tekdemo/PCB-Crown/gerber-previews/crown-B.board-bottom.diff.png

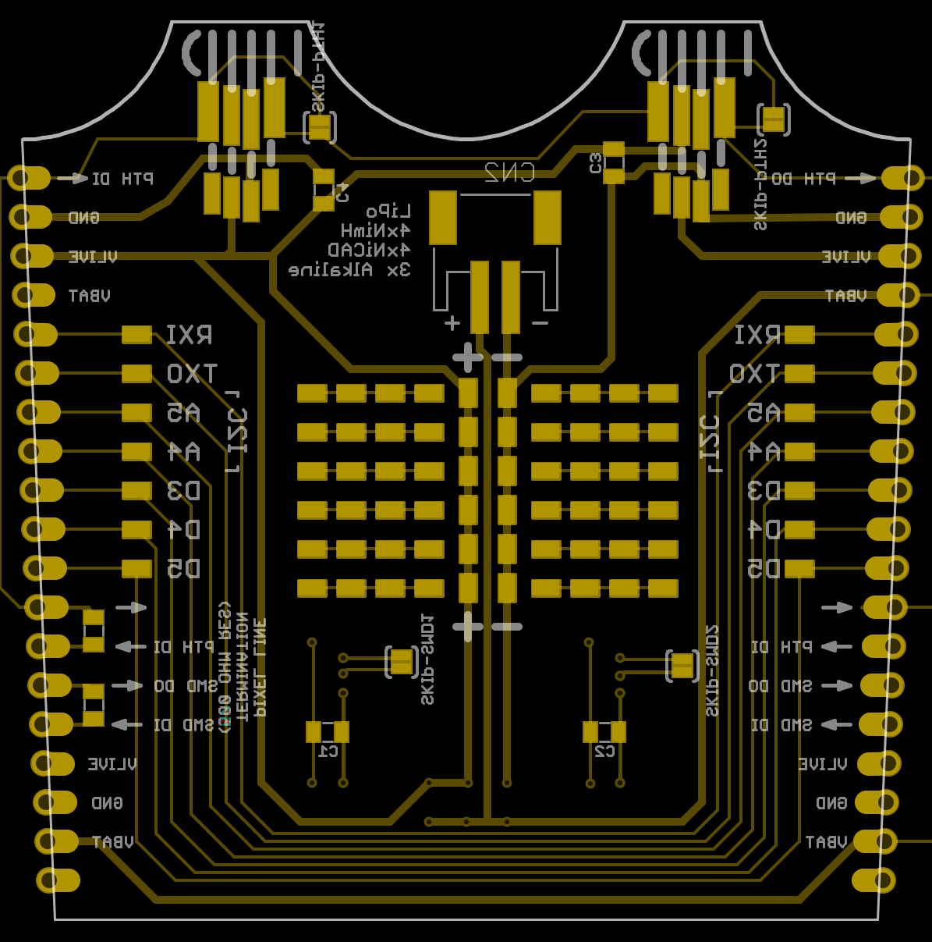
gerber-previews/crown-B.board-bottom.diff.png
