tekdemo/PCB-Crown/gerber-previews/crown-B.board-top.diff.png

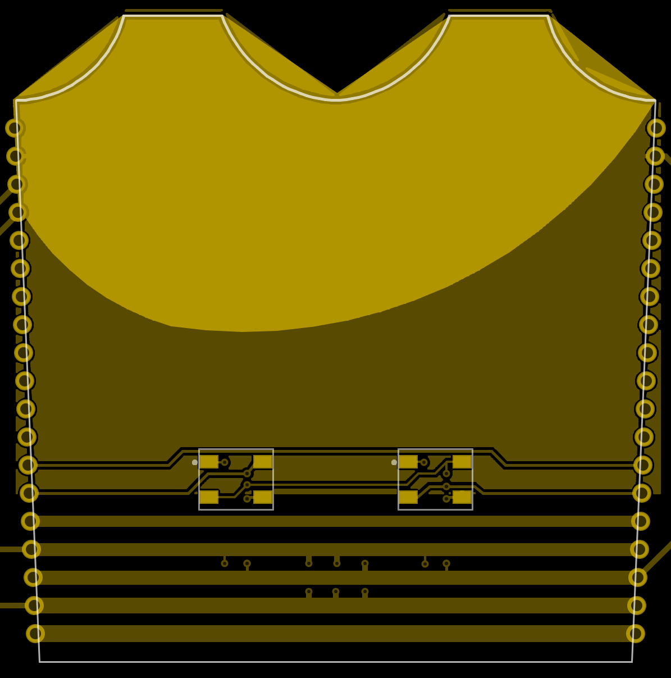
gerber-previews/crown-B.board-top.diff.png
