tekdemo/PCB-Crown/gerber-previews/crown-B.boardoutline.diff.png

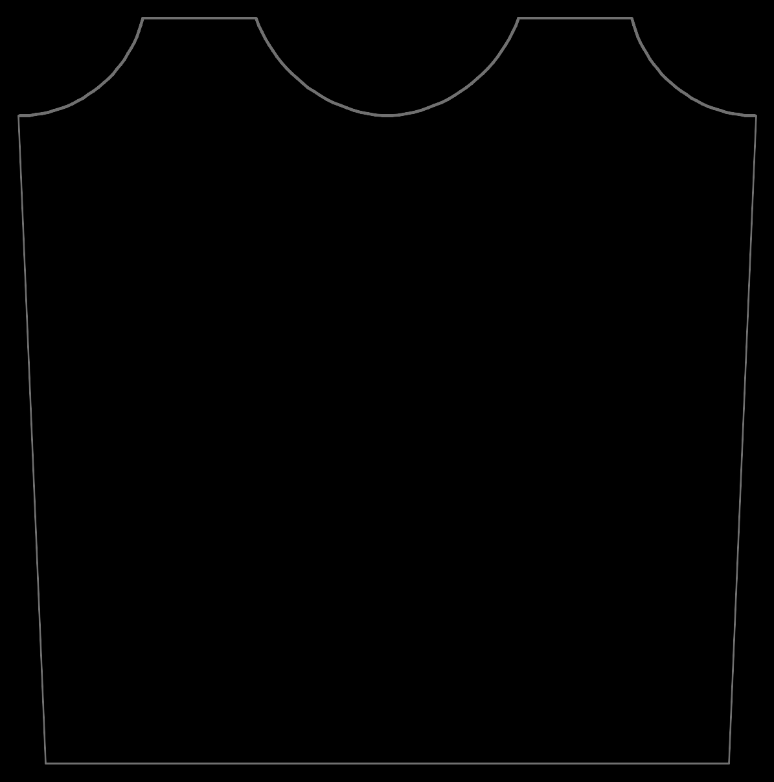
gerber-previews/crown-B.boardoutline.diff.png
