tekdemo/PCB-Crown/gerber-previews/crown-B.bottomlayer.diff.png

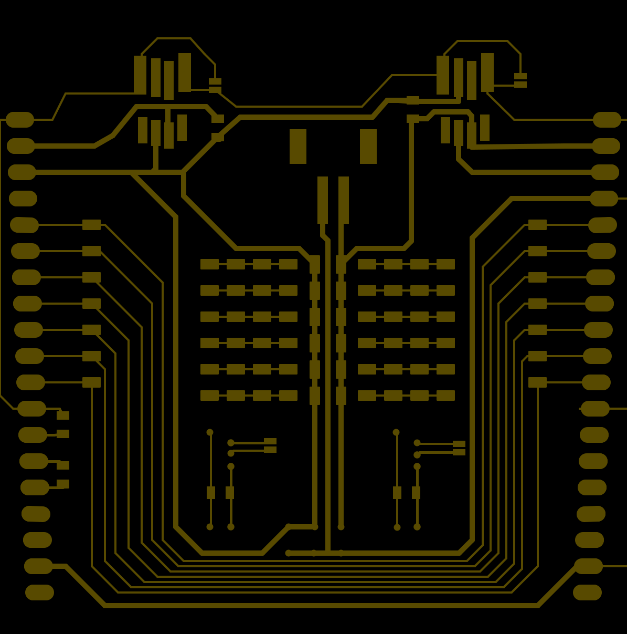
gerber-previews/crown-B.bottomlayer.diff.png
