tekdemo/PCB-Crown/gerber-previews/crown-B.bottomsilkscreen.diff.png

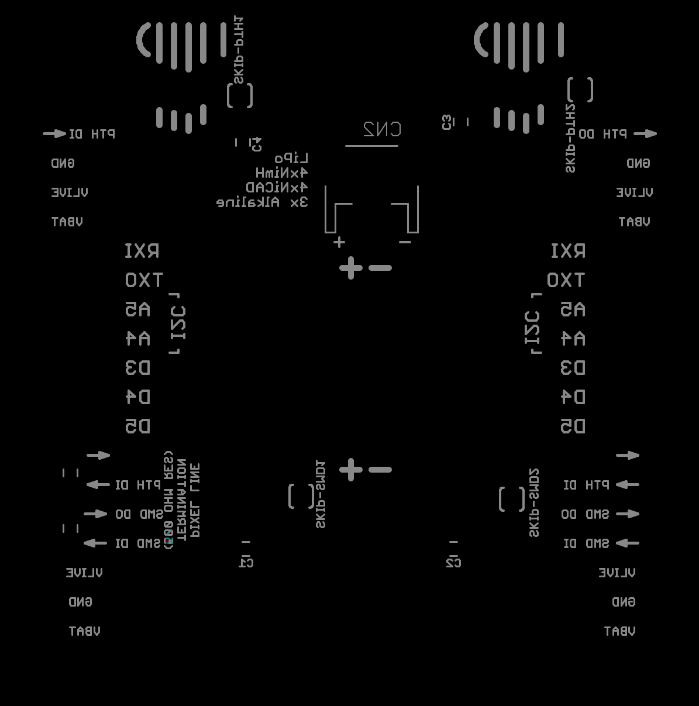
gerber-previews/crown-B.bottomsilkscreen.diff.png
