tekdemo/PCB-Crown/gerber-previews/crown-B.bottomstopmask.diff.png

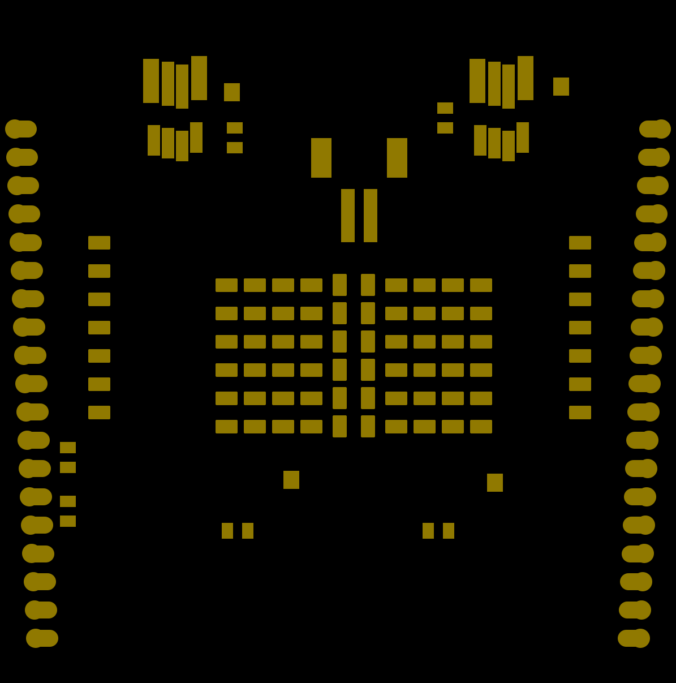
gerber-previews/crown-B.bottomstopmask.diff.png
