tekdemo/PCB-Crown/gerber-previews/crown-B.drills.diff.png

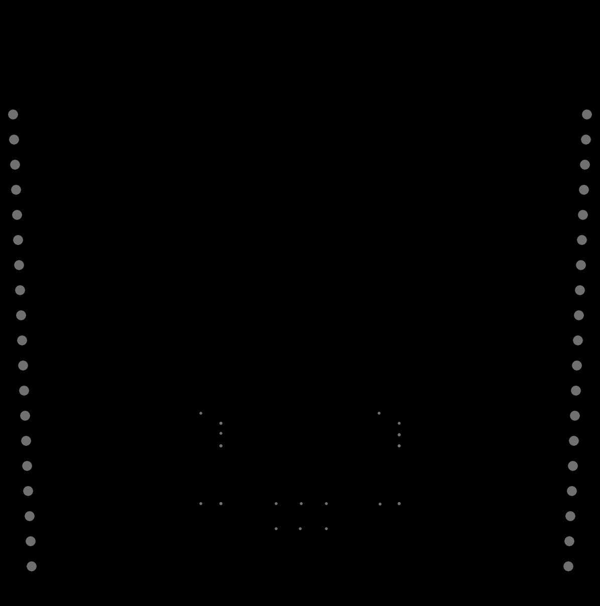
gerber-previews/crown-B.drills.diff.png
