tekdemo/PCB-Crown/gerber-previews/crown-B.toplayer.diff.png

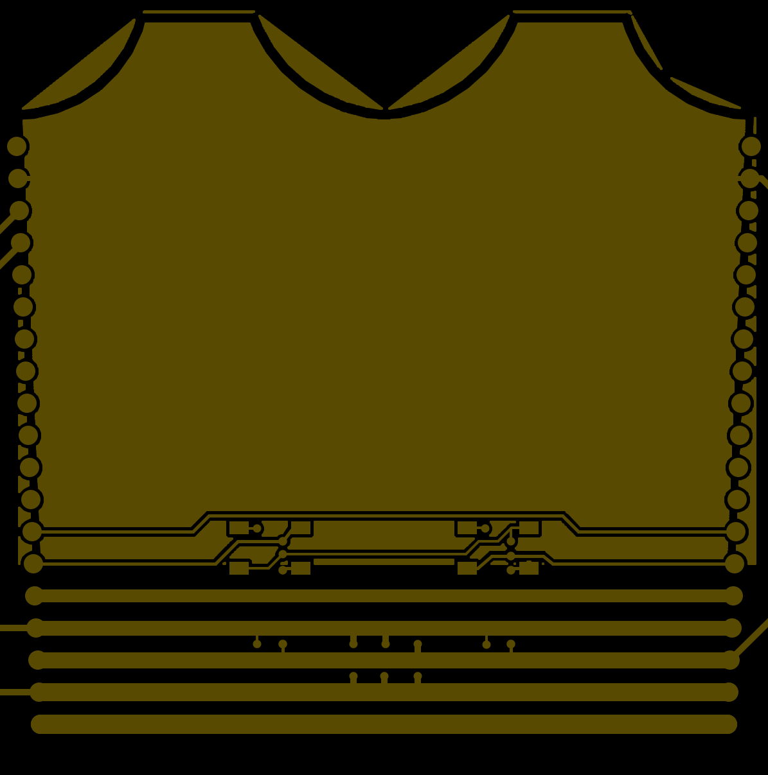
gerber-previews/crown-B.toplayer.diff.png
