tekdemo/PCB-Crown/gerber-previews/crown-B.topsilkscreen.diff.png

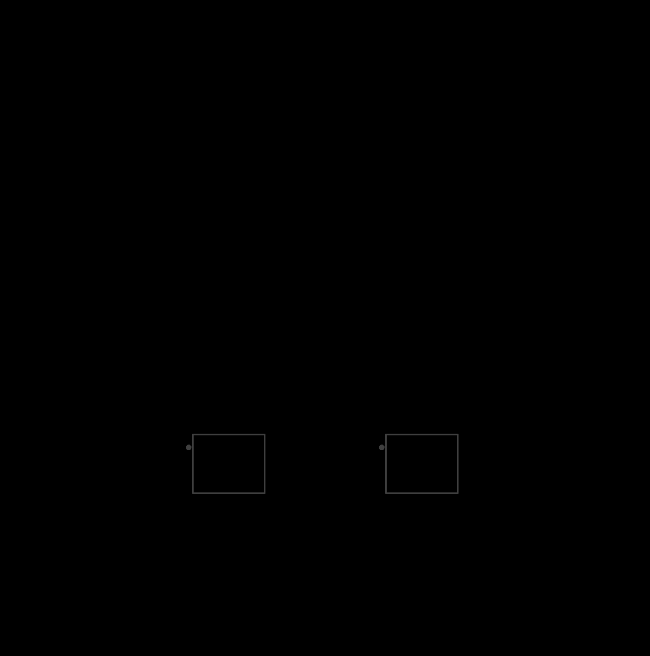
gerber-previews/crown-B.topsilkscreen.diff.png
