tekdemo/PCB-Crown/gerber-previews/crown-B.topstopmask.diff.png

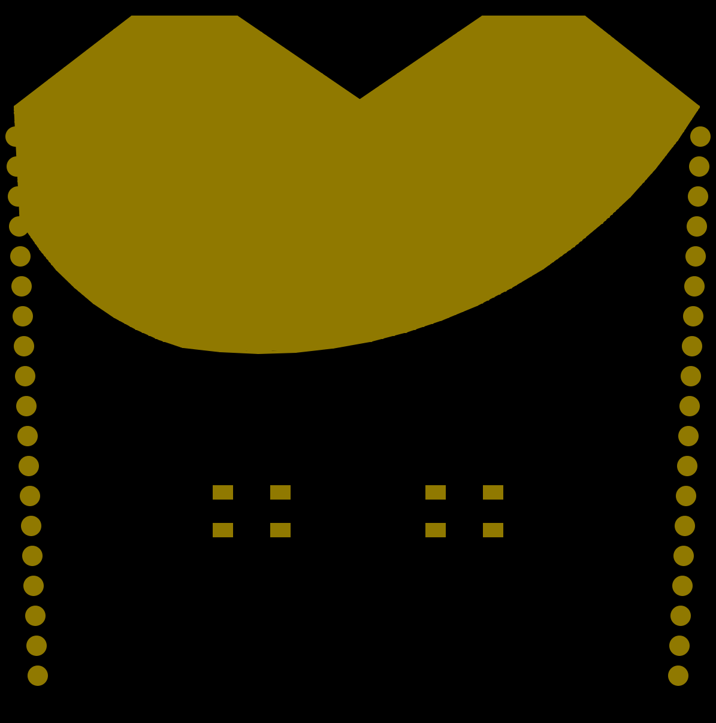
gerber-previews/crown-B.topstopmask.diff.png
