tekdemo/PCB-Crown/gerber-previews/crown-C.board-bottom.diff.png

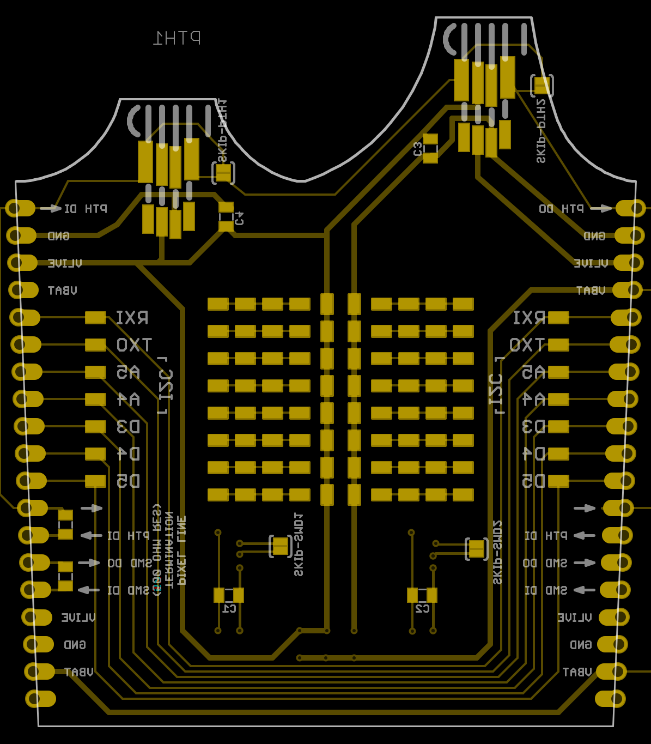
gerber-previews/crown-C.board-bottom.diff.png
