tekdemo/PCB-Crown/gerber-previews/crown-C.board-top.diff.png

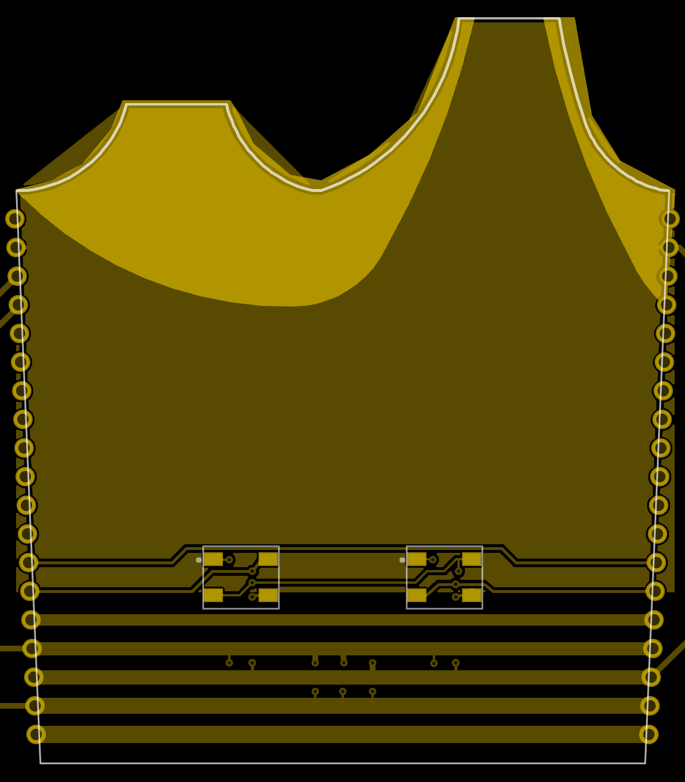
gerber-previews/crown-C.board-top.diff.png
