tekdemo/PCB-Crown/gerber-previews/crown-C.boardoutline.diff.png

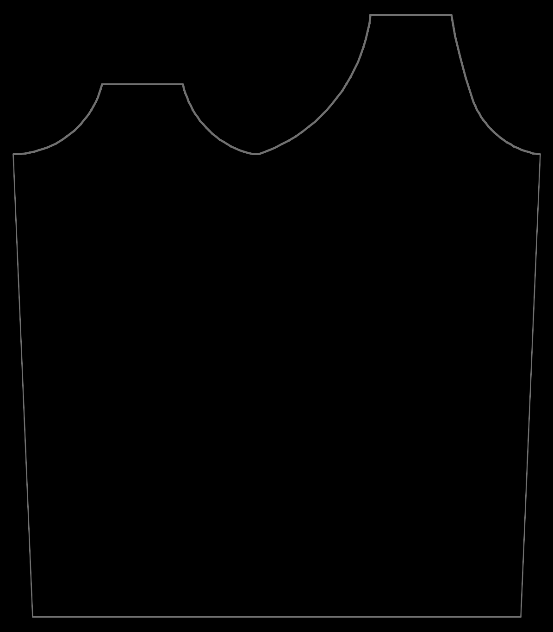
gerber-previews/crown-C.boardoutline.diff.png
