tekdemo/PCB-Crown/gerber-previews/crown-C.bottomlayer.diff.png

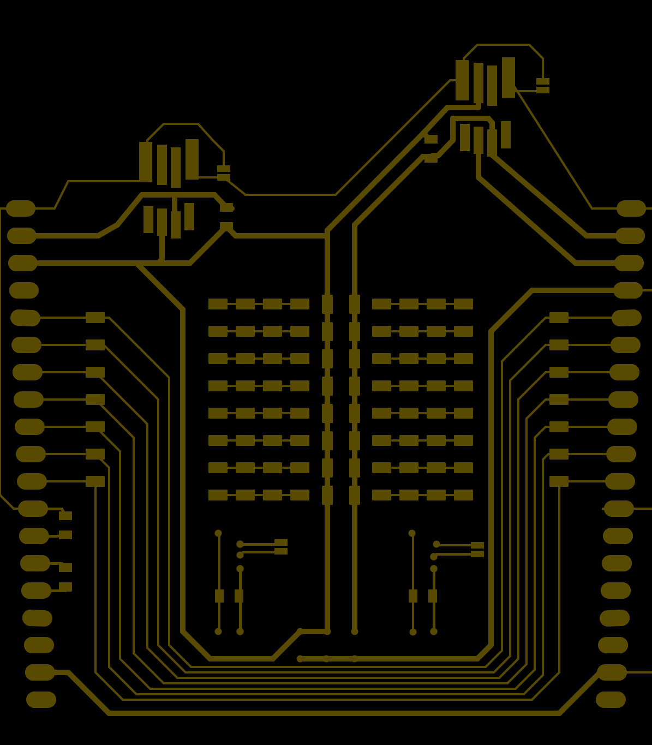
gerber-previews/crown-C.bottomlayer.diff.png
