tekdemo/PCB-Crown/gerber-previews/crown-C.bottomsilkscreen.diff.png

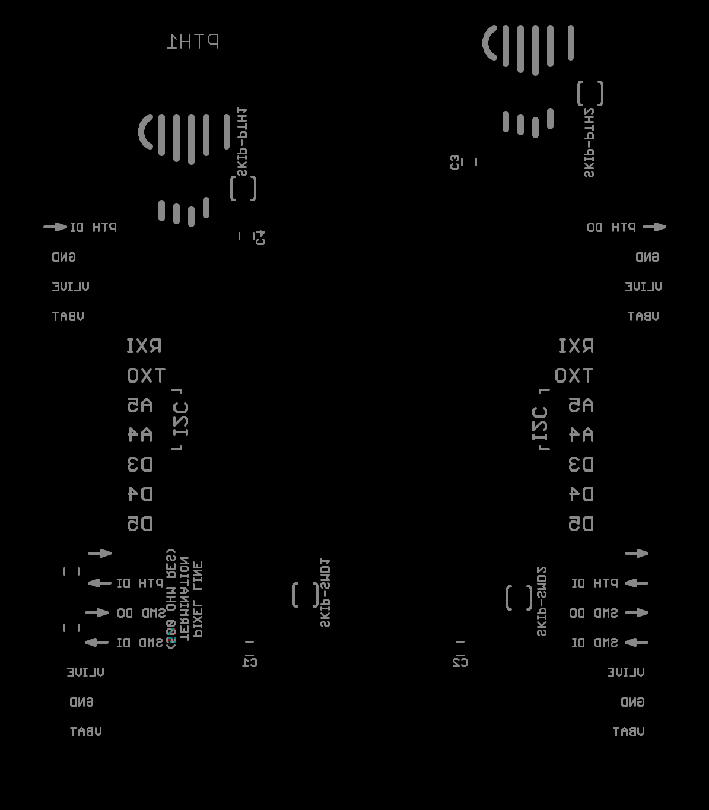
gerber-previews/crown-C.bottomsilkscreen.diff.png
