tekdemo/PCB-Crown/gerber-previews/crown-C.bottomstopmask.diff.png

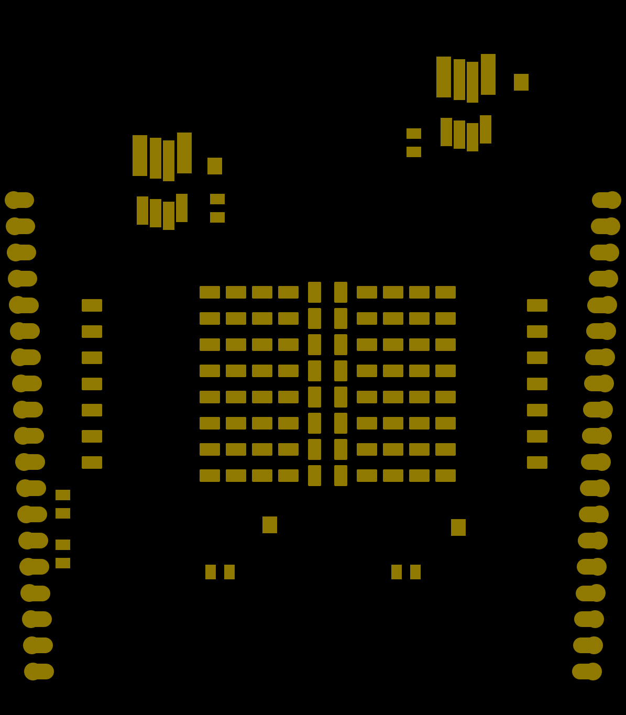
gerber-previews/crown-C.bottomstopmask.diff.png
