tekdemo/PCB-Crown/gerber-previews/crown-C.drills.diff.png

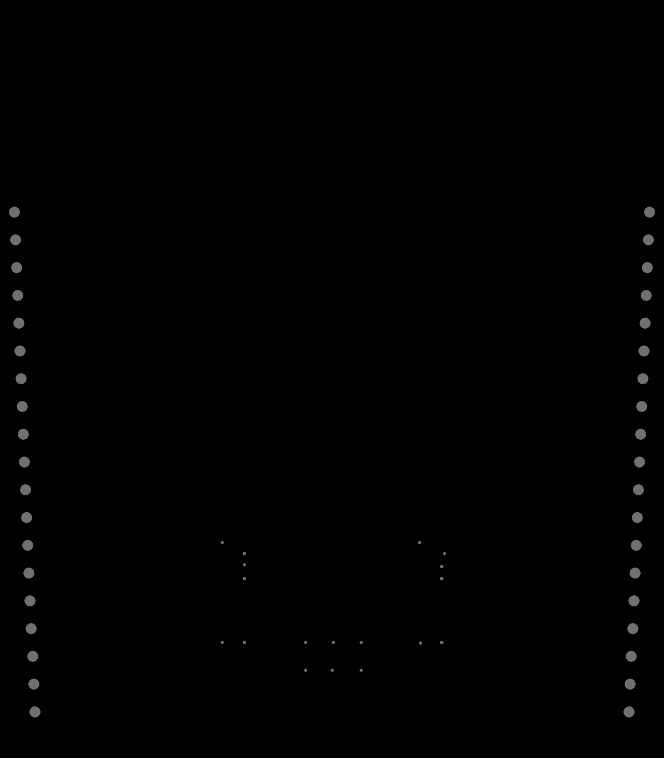
gerber-previews/crown-C.drills.diff.png
