tekdemo/PCB-Crown/gerber-previews/crown-C.toplayer.diff.png

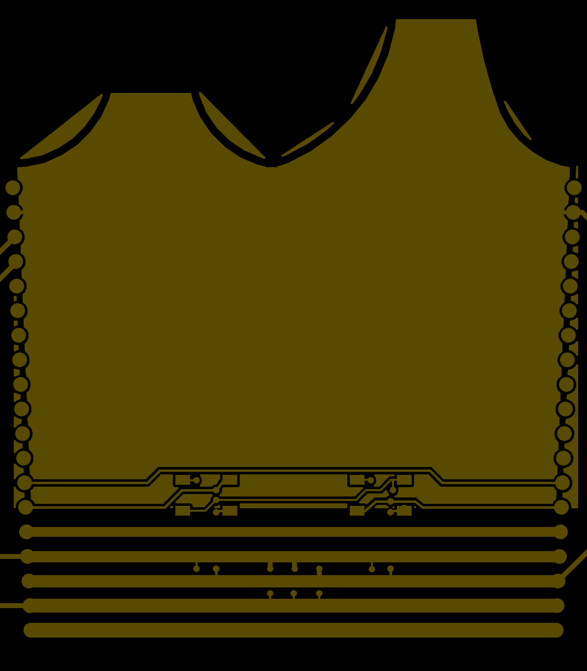
gerber-previews/crown-C.toplayer.diff.png
