tekdemo/PCB-Crown/gerber-previews/crown-C.topstopmask.diff.png

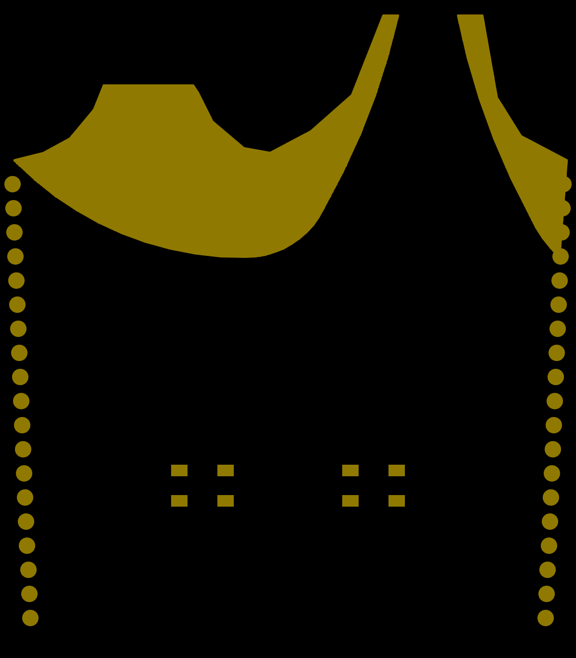
gerber-previews/crown-C.topstopmask.diff.png
