tekdemo/PCB-Crown/gerber-previews/crown-E.board-bottom.diff.png

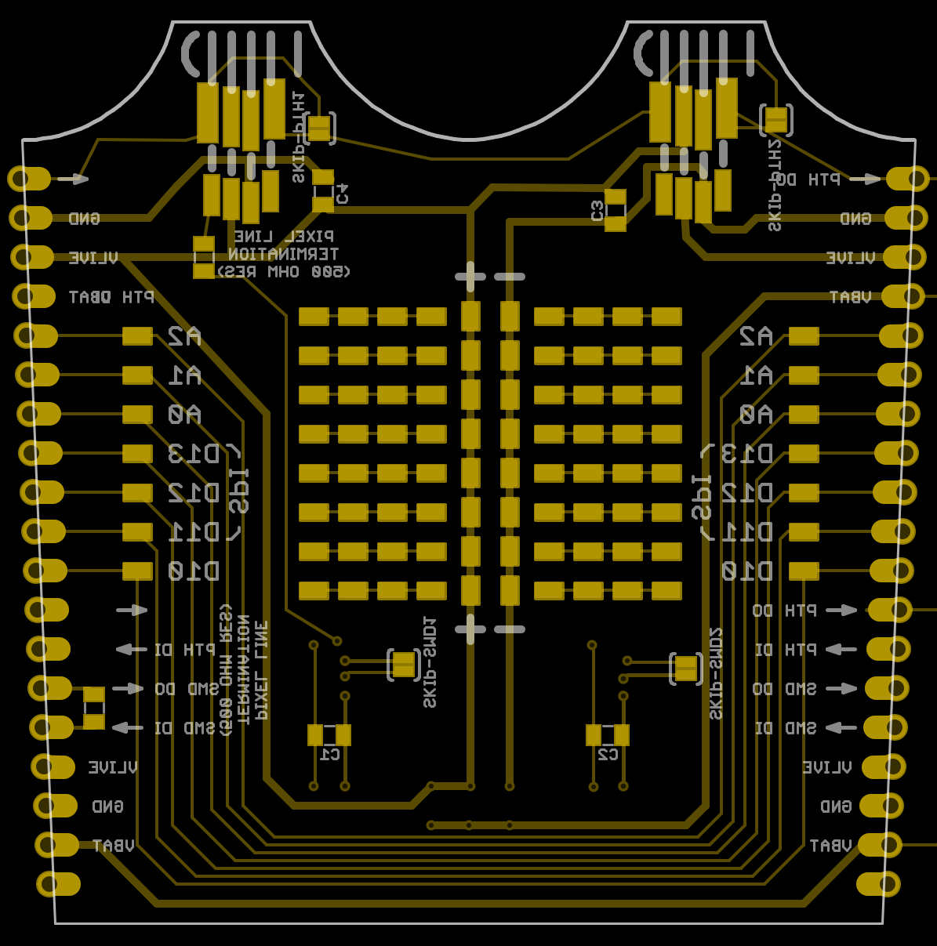
gerber-previews/crown-E.board-bottom.diff.png
