tekdemo/PCB-Crown/gerber-previews/crown-E.board-top.diff.png

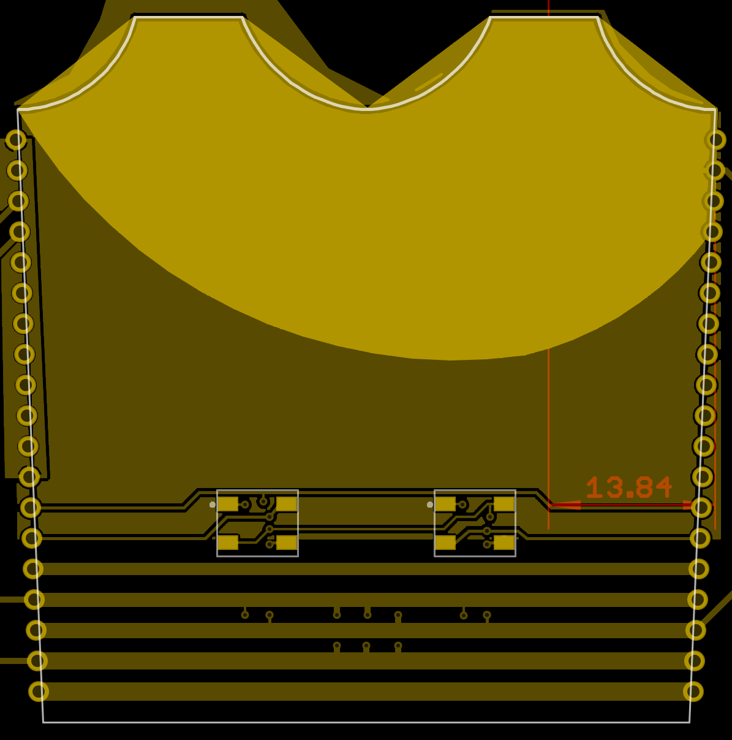
gerber-previews/crown-E.board-top.diff.png
