tekdemo/PCB-Crown/gerber-previews/crown-E.bottomlayer.diff.png

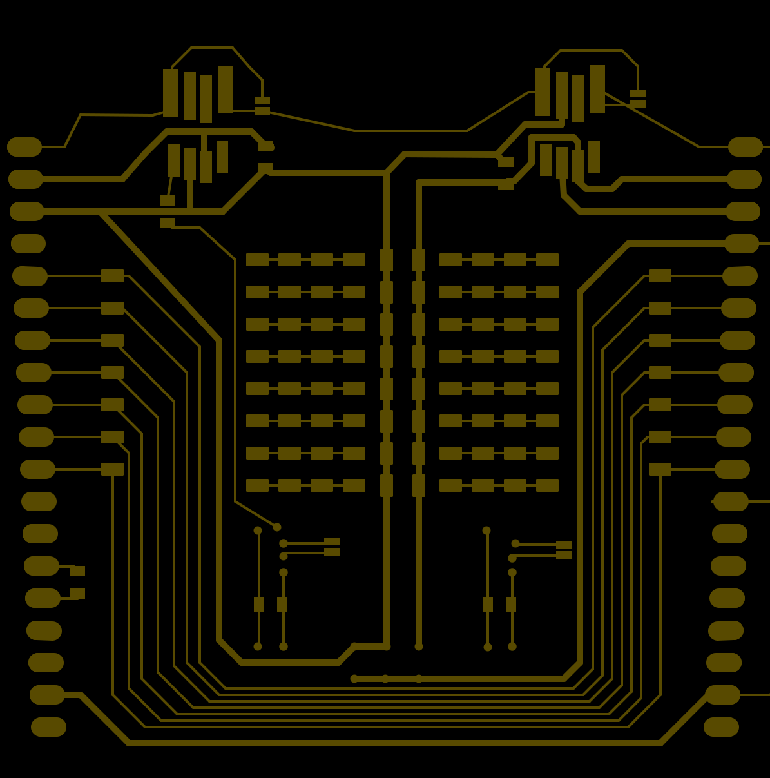
gerber-previews/crown-E.bottomlayer.diff.png
