tekdemo/PCB-Crown/gerber-previews/crown-E.bottomsilkscreen.diff.png

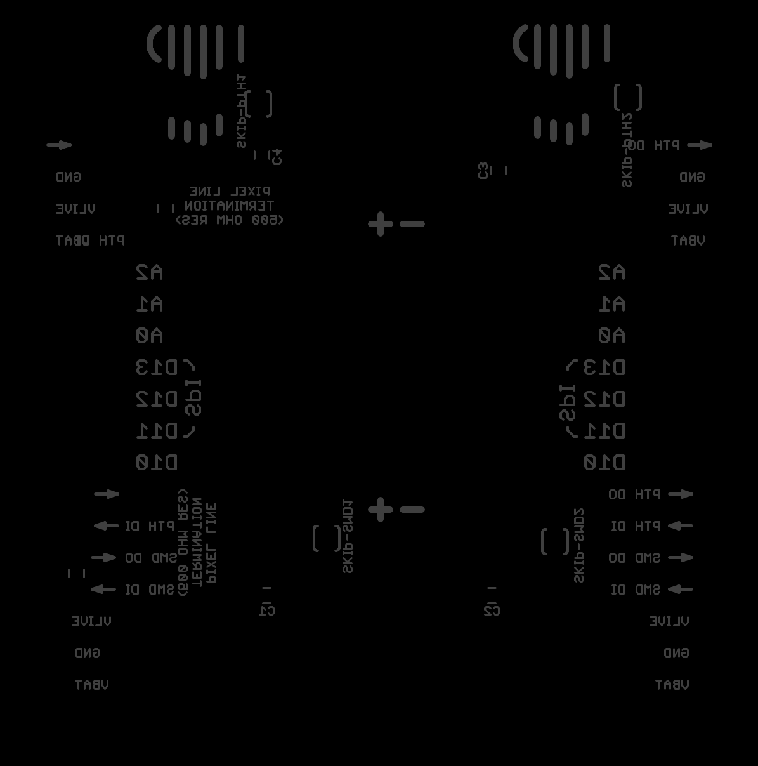
gerber-previews/crown-E.bottomsilkscreen.diff.png
