tekdemo/PCB-Crown/gerber-previews/crown-E.topstopmask.diff.png

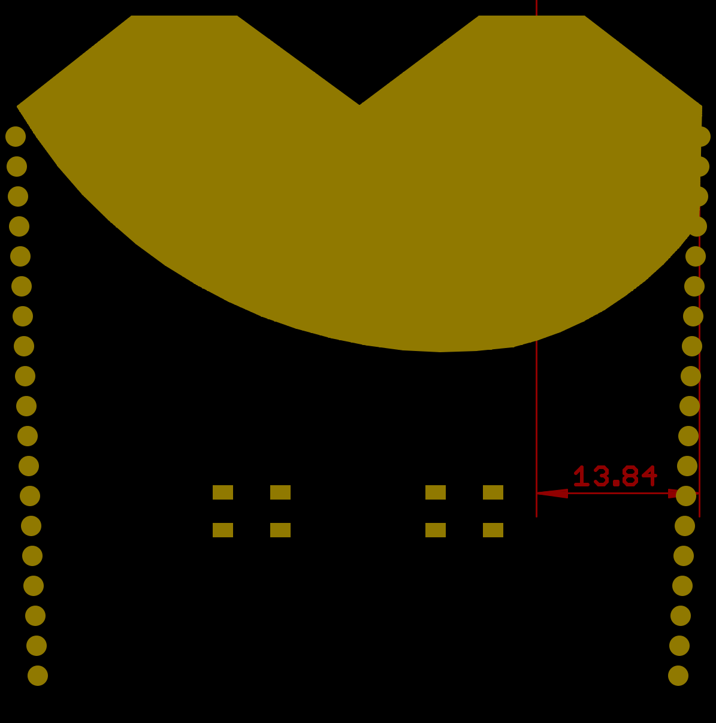
gerber-previews/crown-E.topstopmask.diff.png
