tekdemo/PCB-Crown/gerber-previews/crown-F.board-bottom.diff.png

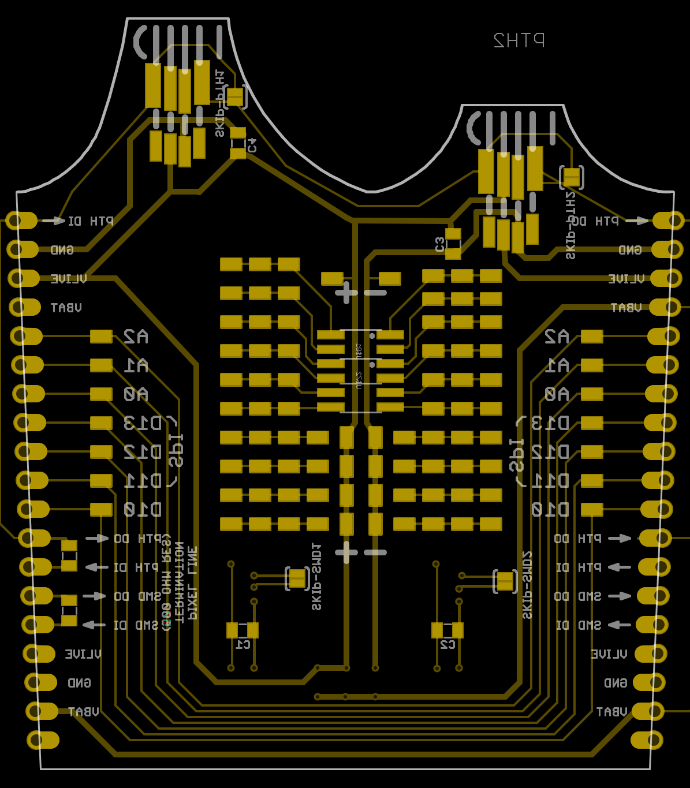
gerber-previews/crown-F.board-bottom.diff.png
