tekdemo/PCB-Crown/gerber-previews/crown-F.board-top.diff.png

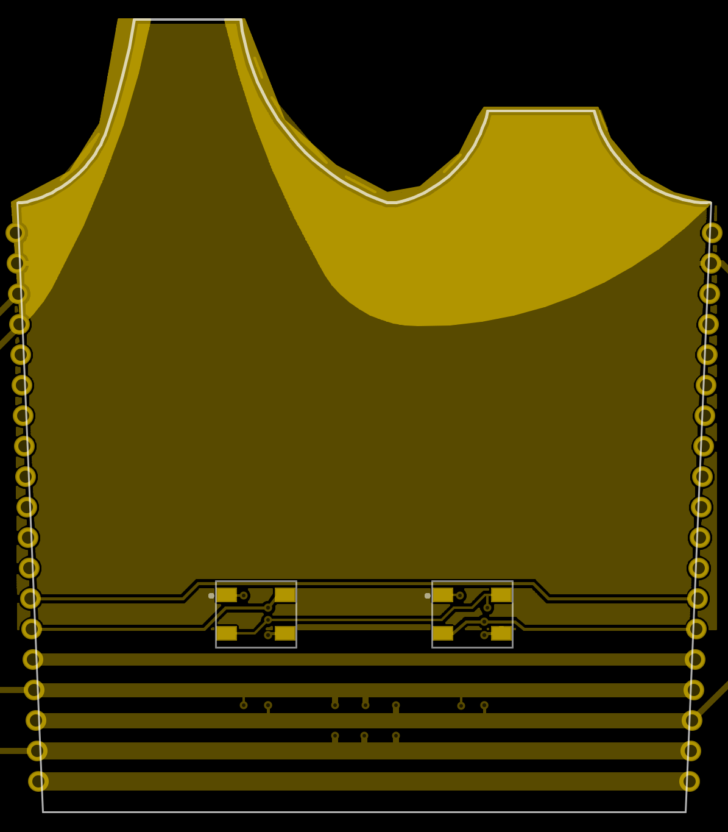
gerber-previews/crown-F.board-top.diff.png
