tekdemo/PCB-Crown/gerber-previews/crown-F.boardoutline.diff.png

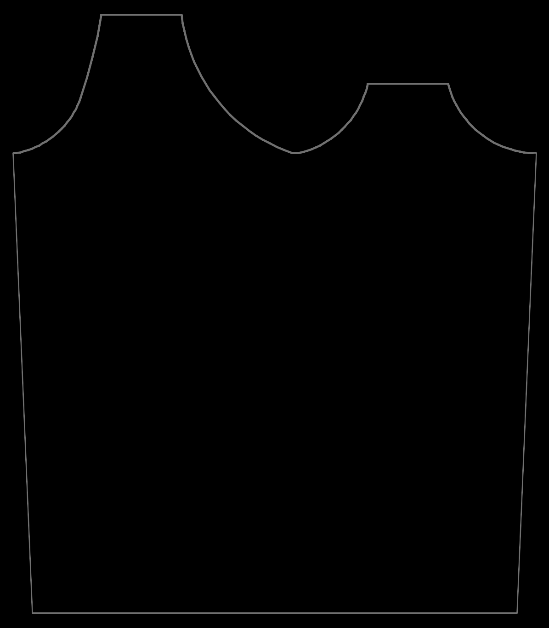
gerber-previews/crown-F.boardoutline.diff.png
