tekdemo/PCB-Crown/gerber-previews/crown-F.bottomlayer.diff.png

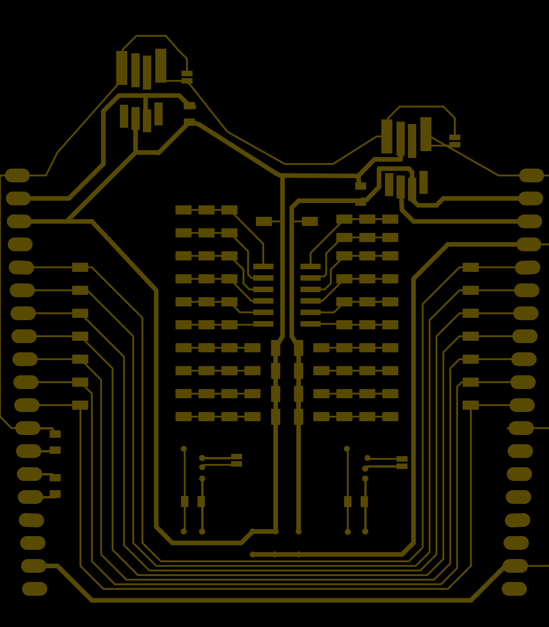
gerber-previews/crown-F.bottomlayer.diff.png
