tekdemo/PCB-Crown/gerber-previews/crown-F.bottomsilkscreen.diff.png

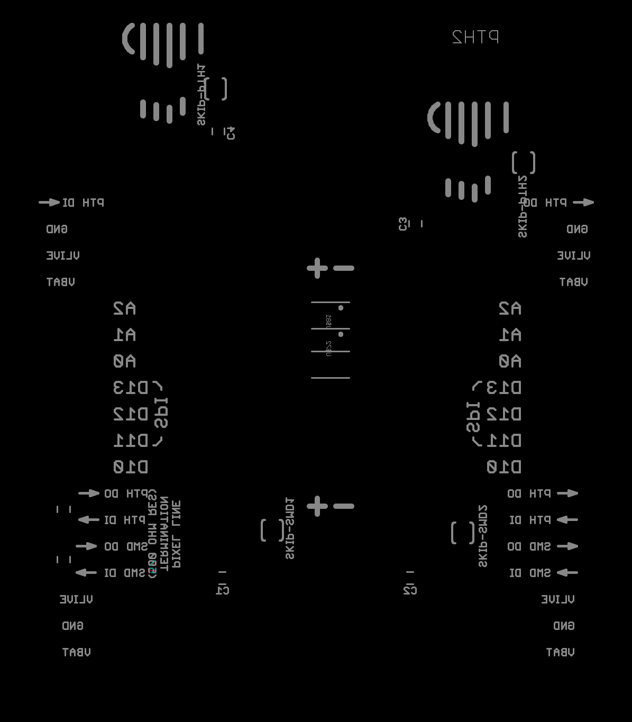
gerber-previews/crown-F.bottomsilkscreen.diff.png
