tekdemo/PCB-Crown/gerber-previews/crown-F.bottomstopmask.diff.png

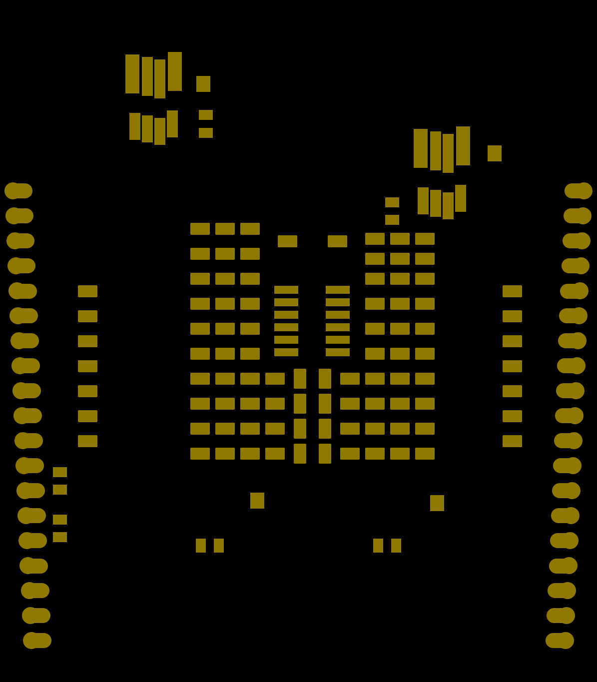
gerber-previews/crown-F.bottomstopmask.diff.png
