tekdemo/PCB-Crown/gerber-previews/crown-F.toplayer.diff.png

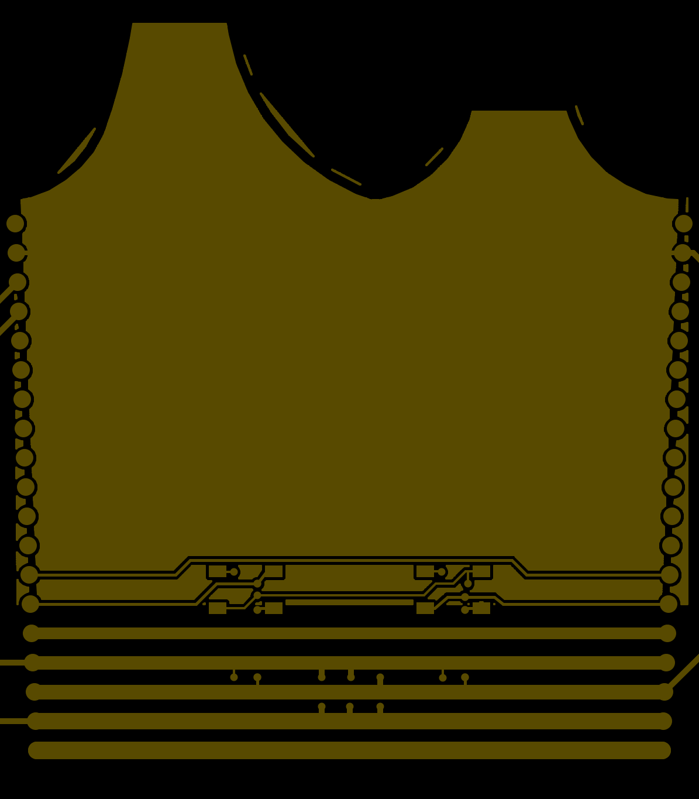
gerber-previews/crown-F.toplayer.diff.png
