tekdemo/PCB-Crown/gerber-previews/crown-F.topstopmask.diff.png

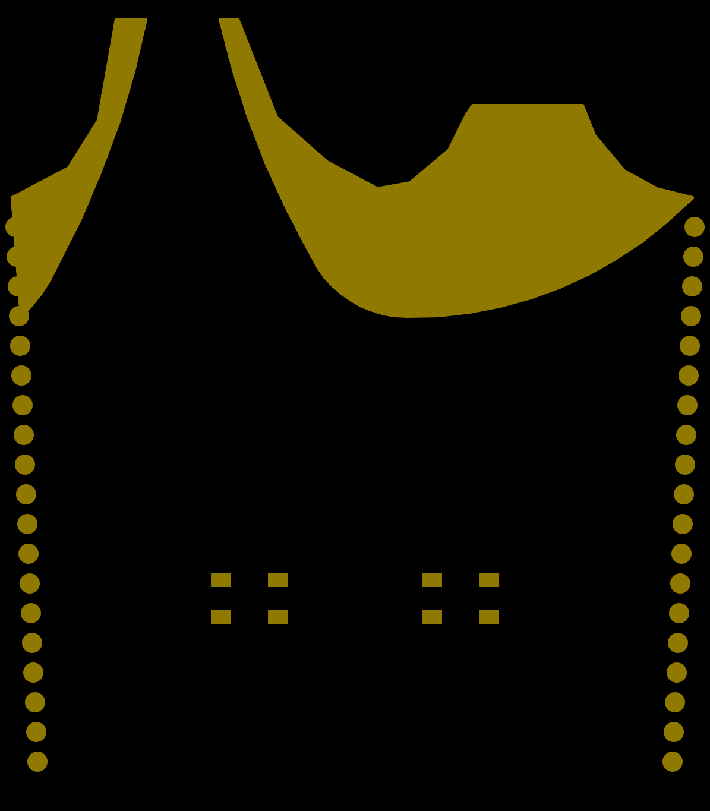
gerber-previews/crown-F.topstopmask.diff.png
