tekdemo/PCB-Crown/gerber-previews/crown-face.board-bottom.diff.png

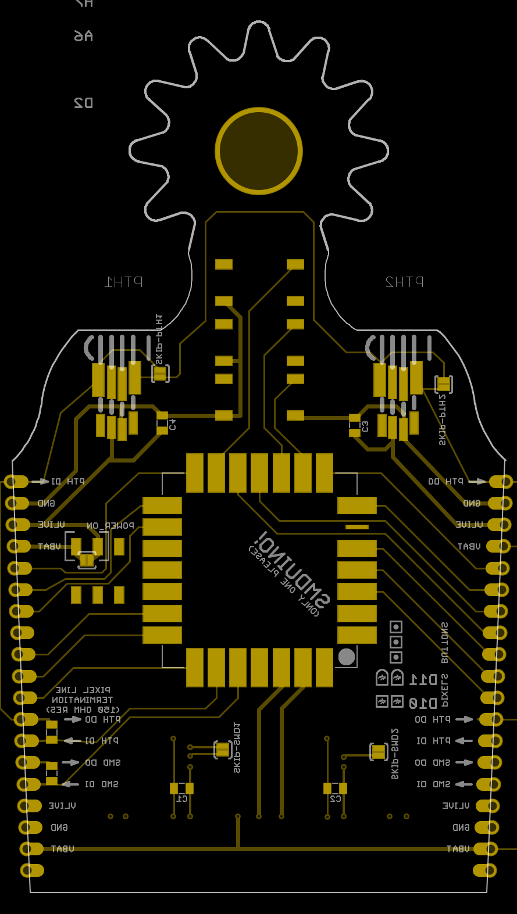
gerber-previews/crown-face.board-bottom.diff.png
