tekdemo/PCB-Crown/gerber-previews/crown-face.board-bottom.png

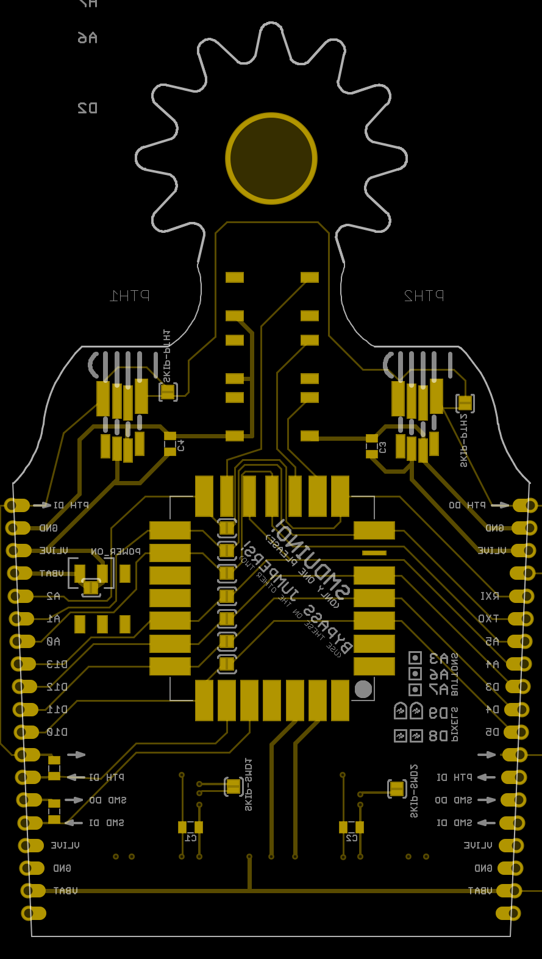
gerber-previews/crown-face.board-bottom.png
