tekdemo/PCB-Crown/gerber-previews/crown-face.board-top.diff.png

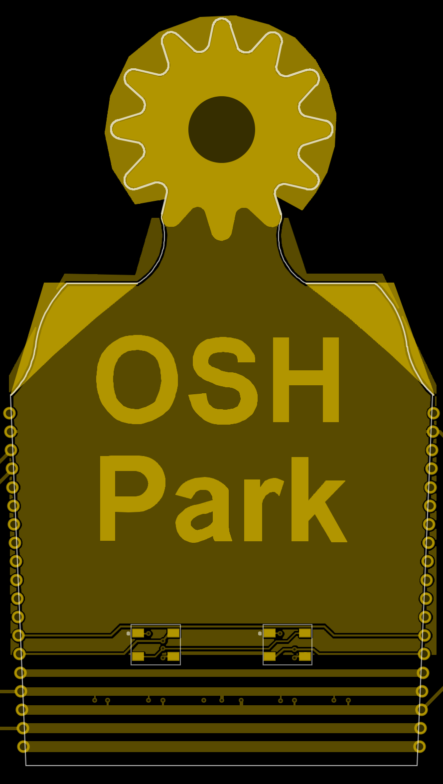
gerber-previews/crown-face.board-top.diff.png
