tekdemo/PCB-Crown/gerber-previews/crown-face.boardoutline.diff.png

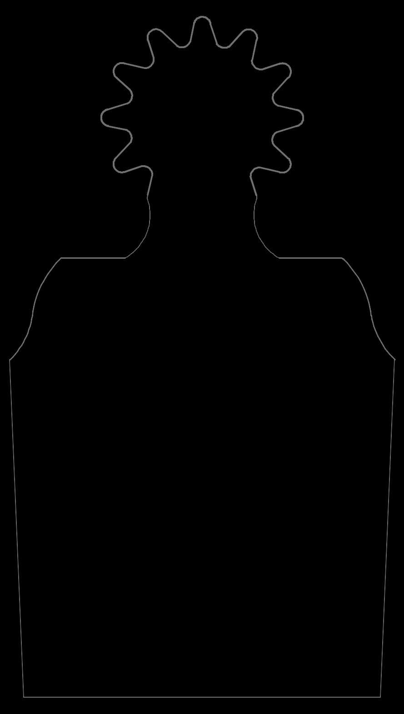
gerber-previews/crown-face.boardoutline.diff.png
