tekdemo/PCB-Crown/gerber-previews/crown-face.bottomlayer.diff.png

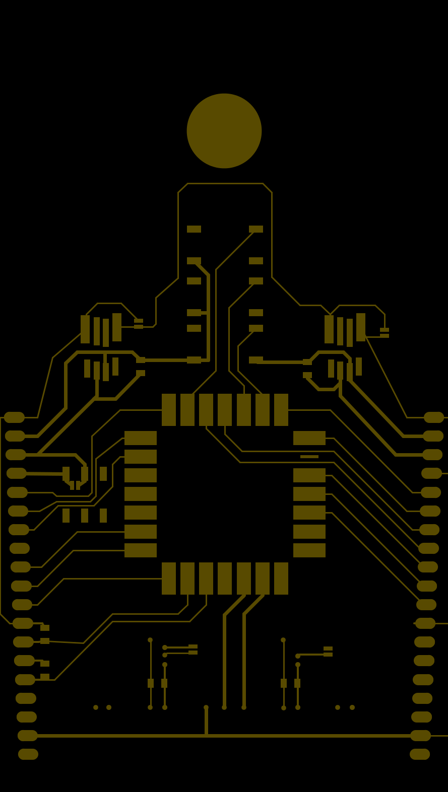
gerber-previews/crown-face.bottomlayer.diff.png
