tekdemo/PCB-Crown/gerber-previews/crown-face.bottomlayer.png

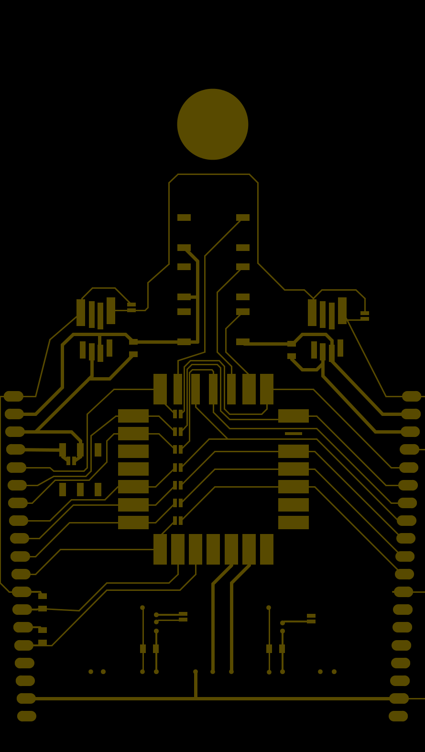
gerber-previews/crown-face.bottomlayer.png
