tekdemo/PCB-Crown/gerber-previews/crown-face.bottomsilkscreen.diff.png

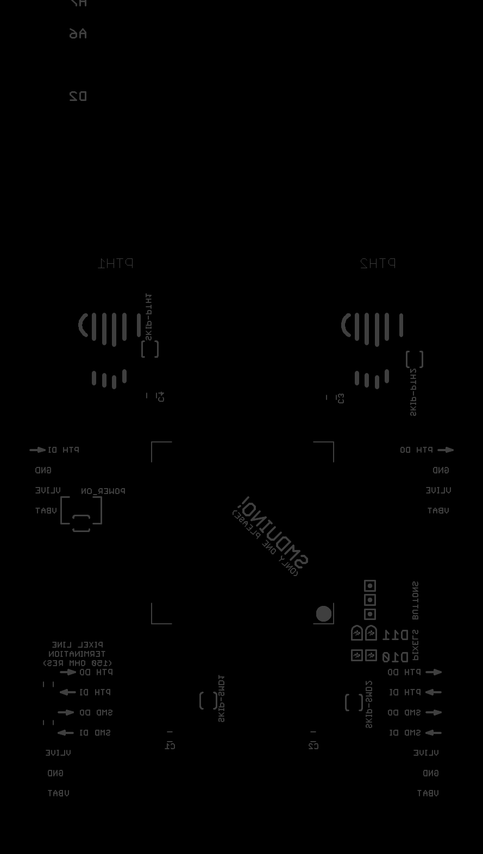
gerber-previews/crown-face.bottomsilkscreen.diff.png
