tekdemo/PCB-Crown/gerber-previews/crown-face.bottomsilkscreen.png

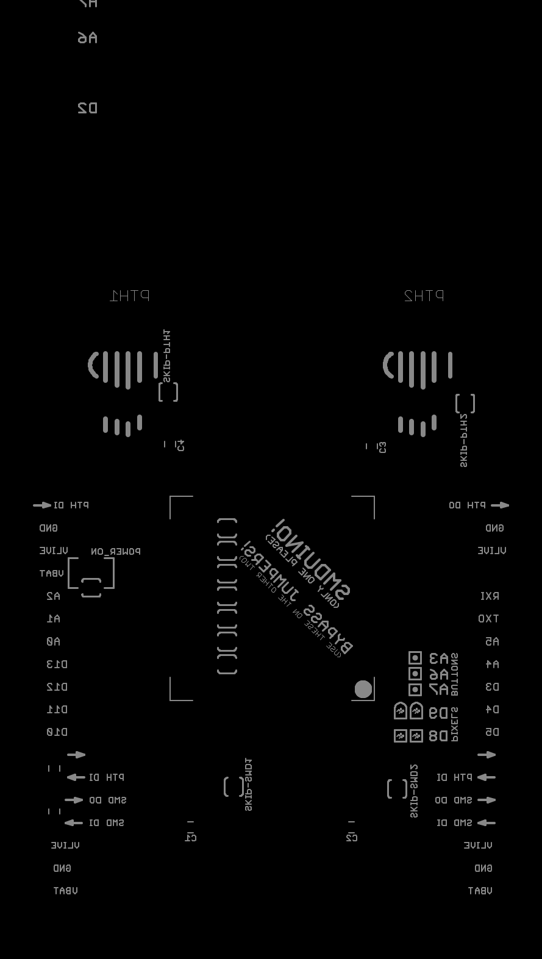
gerber-previews/crown-face.bottomsilkscreen.png
