tekdemo/PCB-Crown/gerber-previews/crown-face.bottomstopmask.diff.png

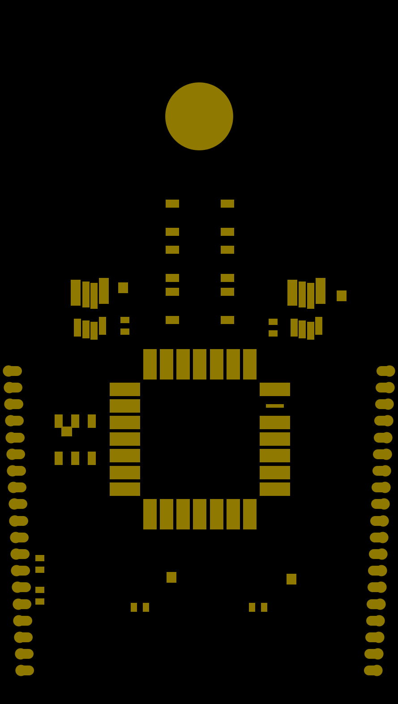
gerber-previews/crown-face.bottomstopmask.diff.png
