tekdemo/PCB-Crown/gerber-previews/crown-face.bottomstopmask.png

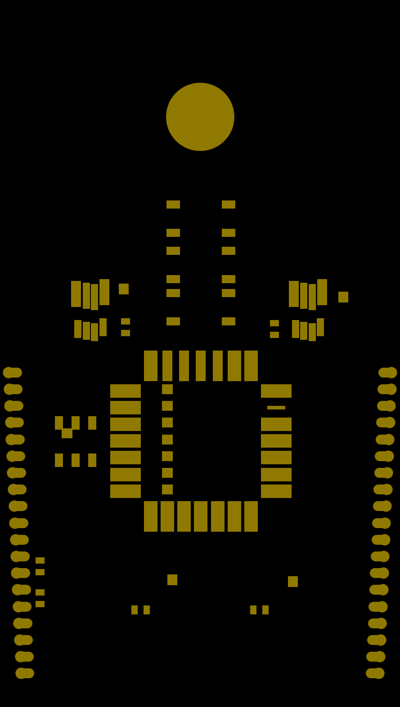
gerber-previews/crown-face.bottomstopmask.png
