tekdemo/PCB-Crown/gerber-previews/crown-face.drills.diff.png

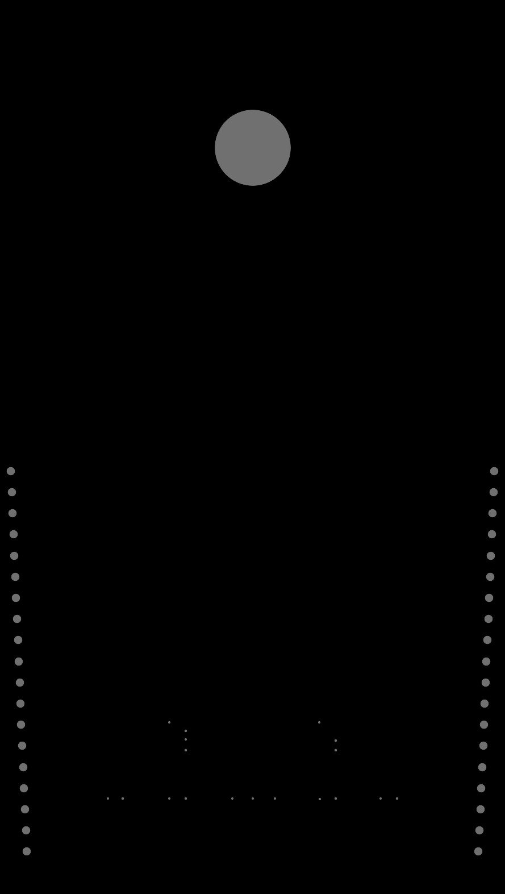
gerber-previews/crown-face.drills.diff.png
