tekdemo/PCB-Crown/gerber-previews/crown-face.topsilkscreen.diff.png

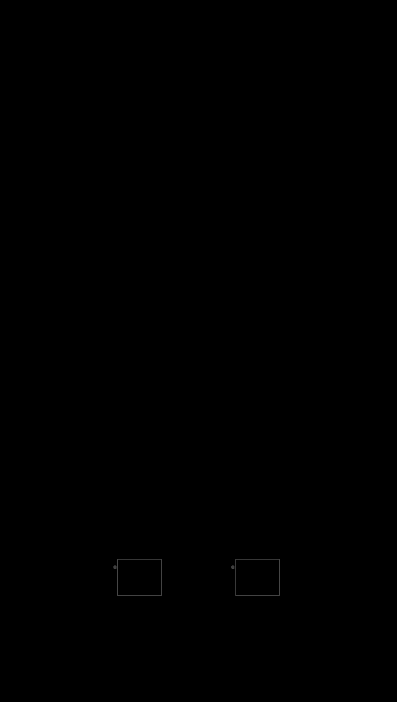
gerber-previews/crown-face.topsilkscreen.diff.png
