tekdemo/PCB-Crown/gerber-previews/crown-face.topstopmask.diff.png

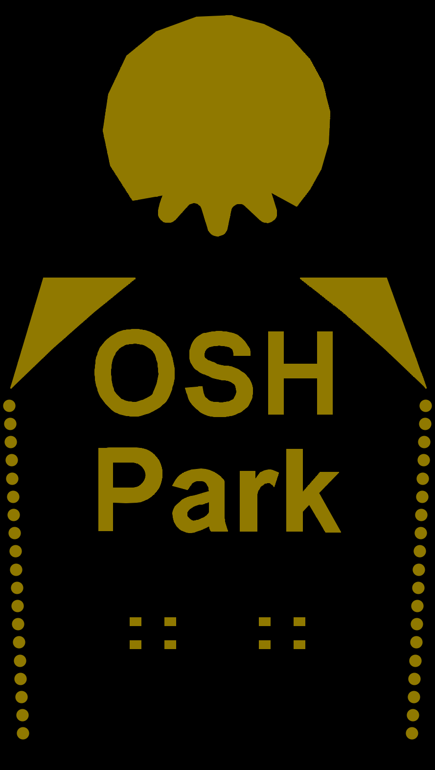
gerber-previews/crown-face.topstopmask.diff.png
