tekdemo/PCB-Crown/gerber-previews/crown-layout.board-bottom.png

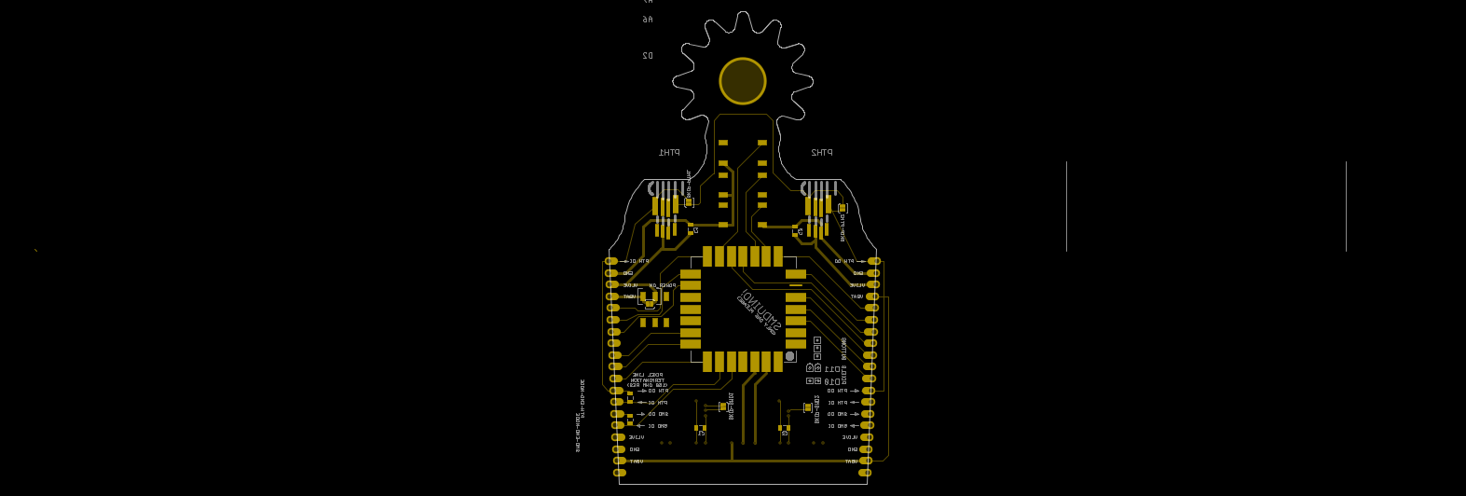
gerber-previews/crown-layout.board-bottom.png
