tekdemo/PCB-Crown/gerber-previews/crown-layout.board-top.png

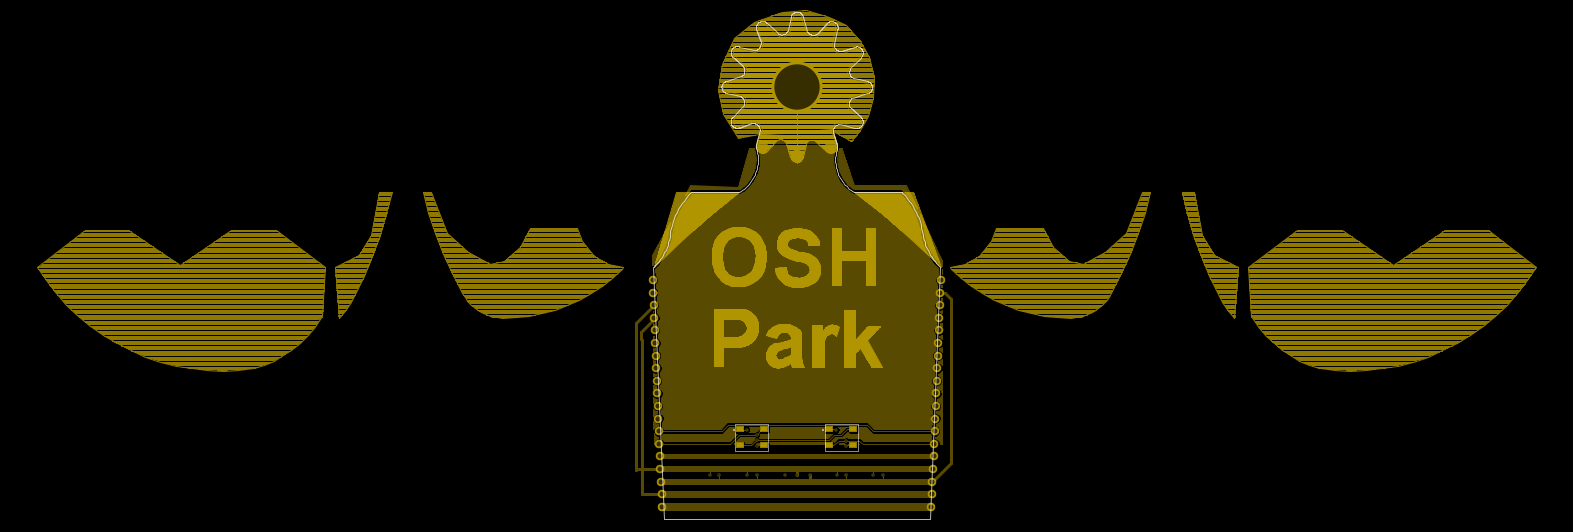
gerber-previews/crown-layout.board-top.png
