tekdemo/PCB-Crown/gerber-previews/crown-layout.boardoutline.png

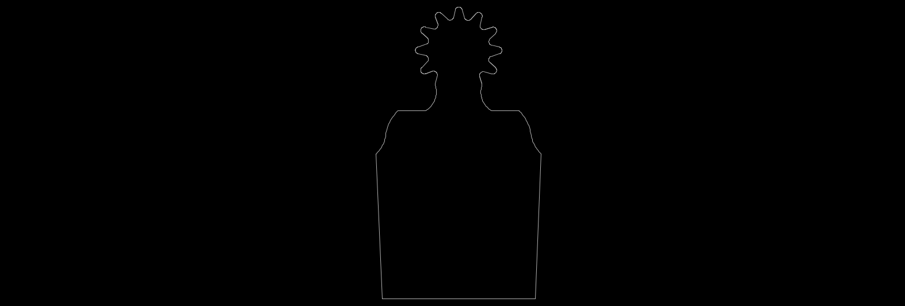
gerber-previews/crown-layout.boardoutline.png
