tekdemo/PCB-Crown/gerber-previews/crown-layout.bottomlayer.png

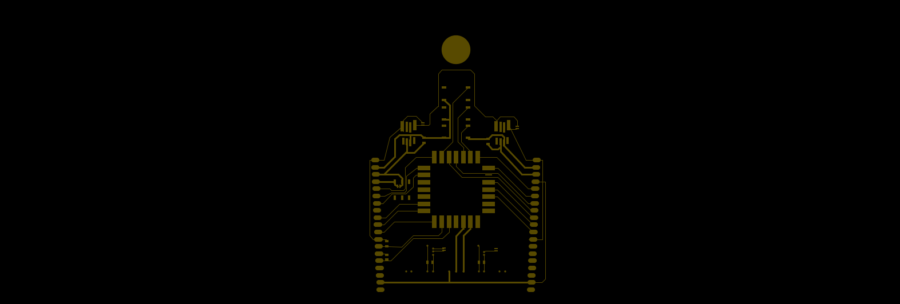
gerber-previews/crown-layout.bottomlayer.png
