tekdemo/PCB-Crown/gerber-previews/crown-layout.bottomsilkscreen.png

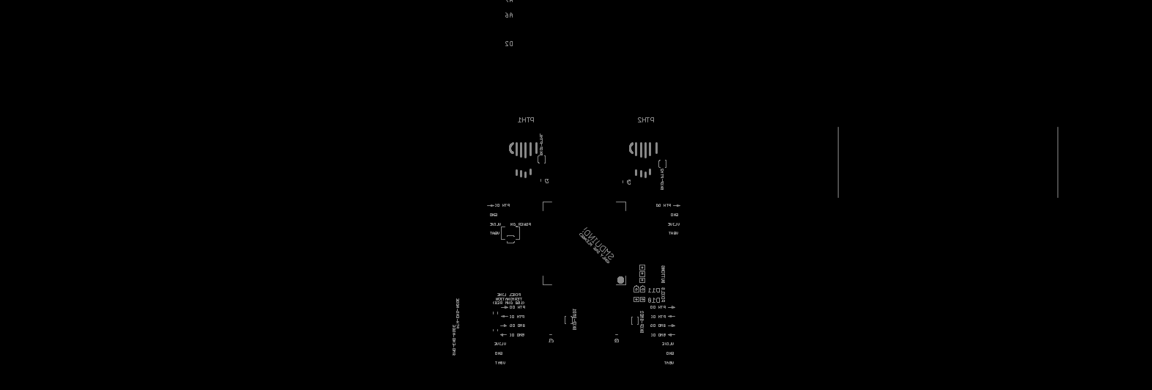
gerber-previews/crown-layout.bottomsilkscreen.png
