tekdemo/PCB-Crown/gerber-previews/crown-layout.bottomstopmask.png

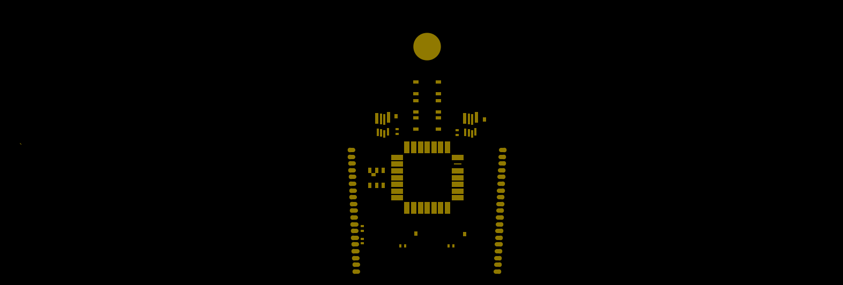
gerber-previews/crown-layout.bottomstopmask.png
