tekdemo/PCB-Crown/gerber-previews/crown-layout.drills.png

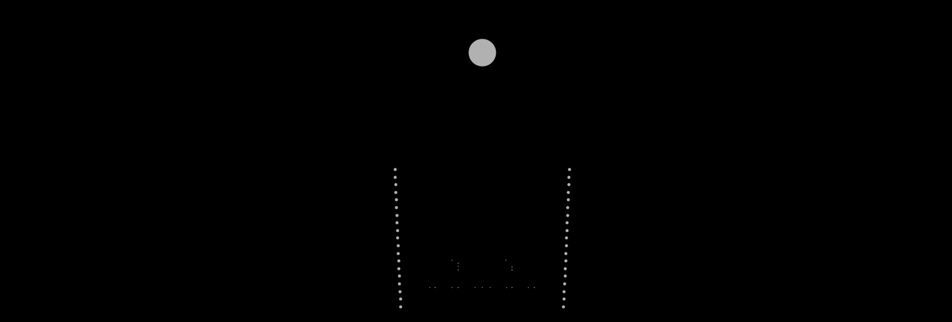
gerber-previews/crown-layout.drills.png
