tekdemo/PCB-Crown/gerber-previews/crown-layout.topstopmask.png

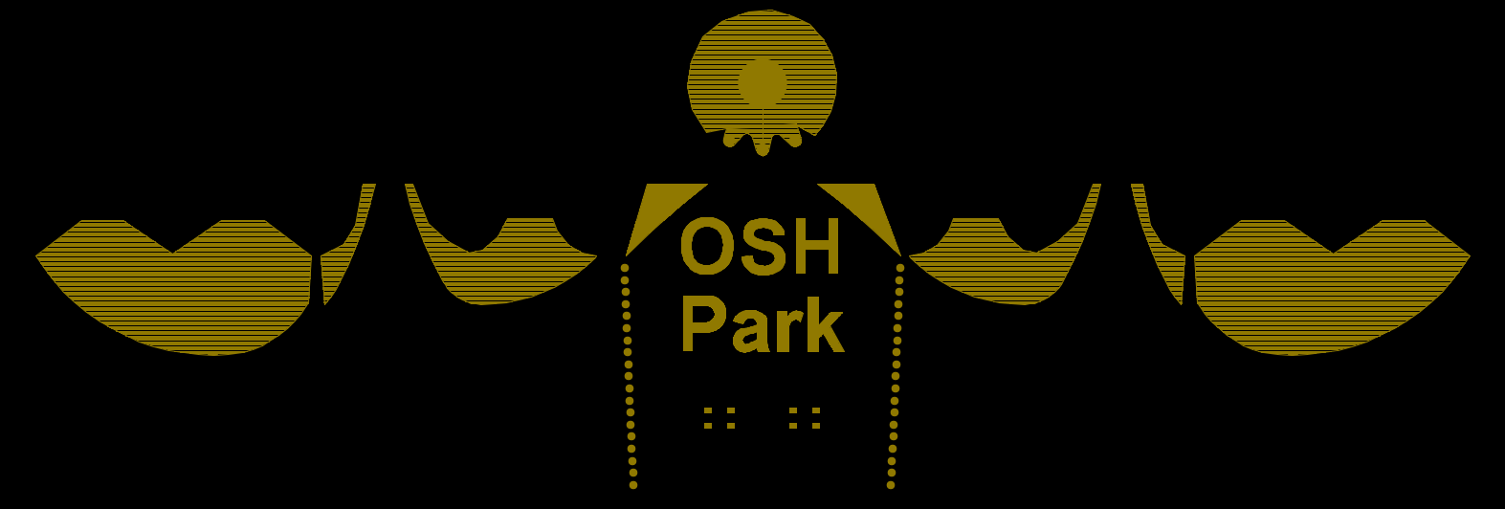
gerber-previews/crown-layout.topstopmask.png
